nojan1/project-wrass/eda/audio-card/audio-card.kicad_pcb

## KiCad design eda/audio-card/audio-card.kicad_pcb (2023-07-22)

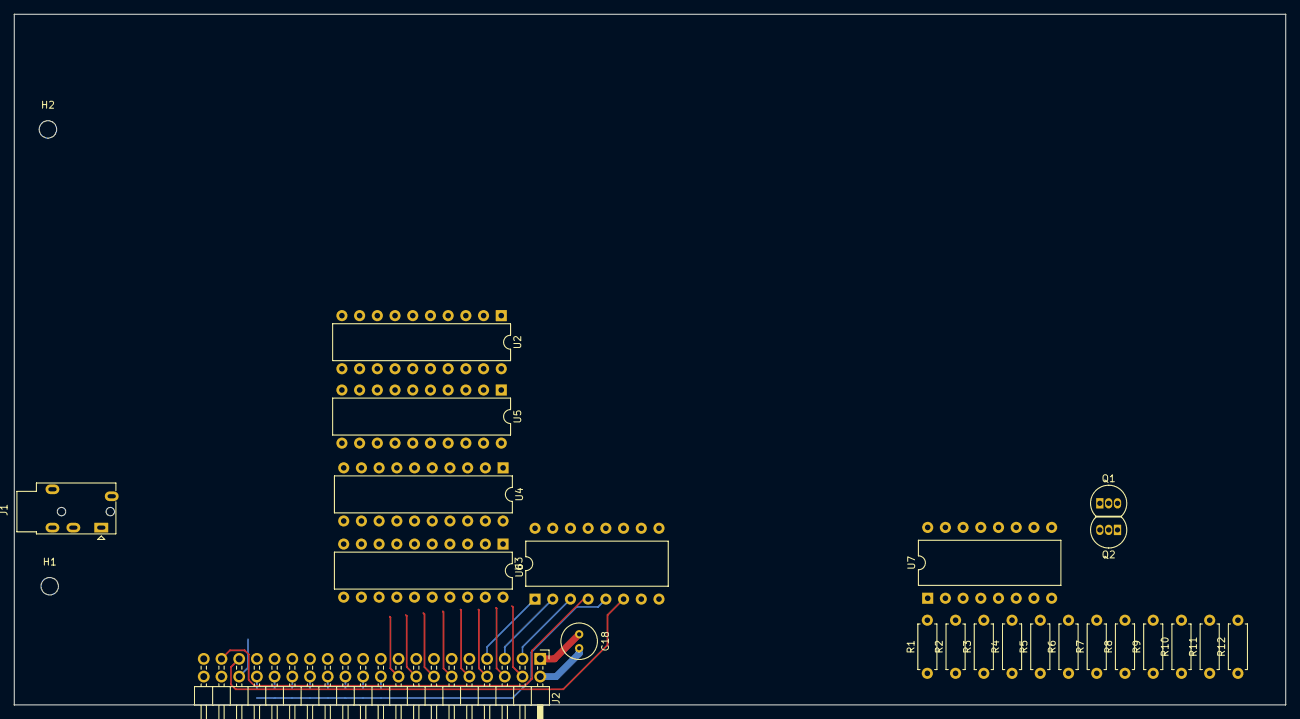
[picture p53: board audio-card.kicad_pcb from above]

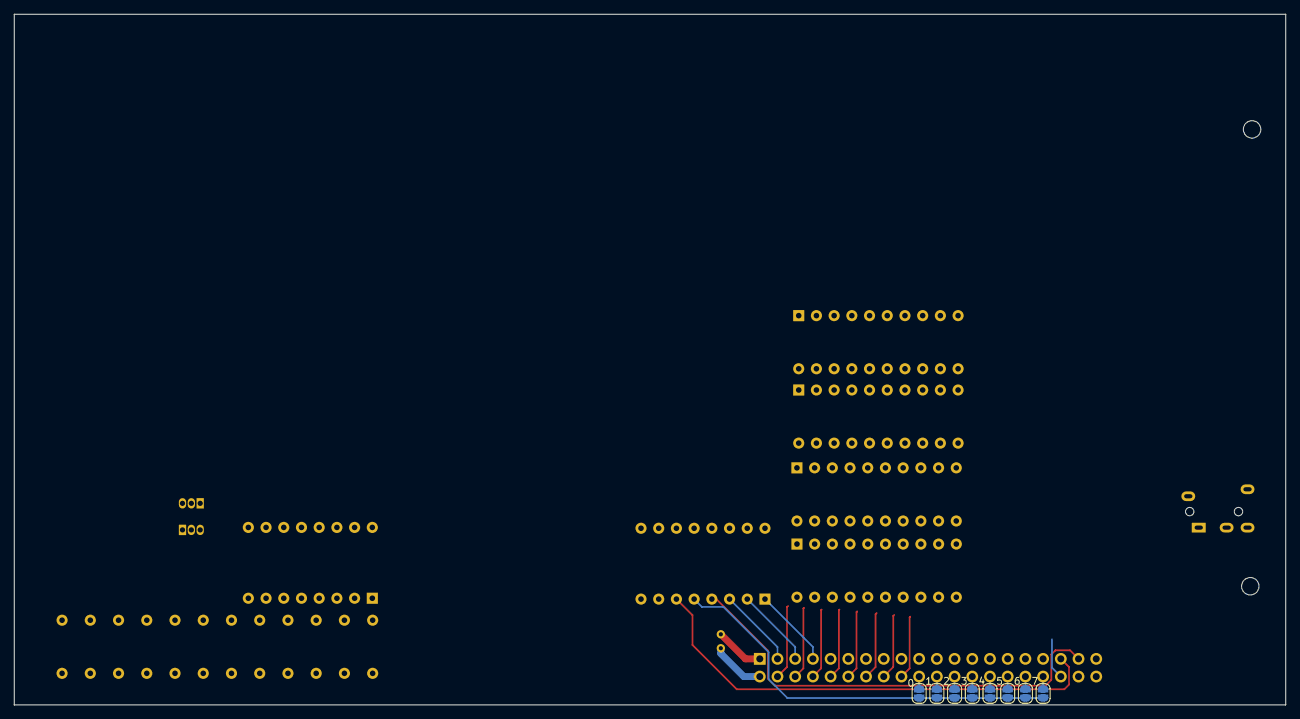
[picture p54: board audio-card.kicad_pcb from below]

Board: 2 copper layers, 182.4 x 99.1 mm, 33 parts (8 on the bottom side), 39 nets.

Parts:
C18: 100nf; C_Radial_D5.0mm_H7.0mm_P2.00mm
H1, H2: Bracket mounting; MountingHole_2.5mm
J1: AudioJack2_SwitchT; Jack_3.5mm_PJ320E_Horizontal
J2: Bus expansion; PinHeader_2x20_P2.54mm_Horizontal
JP1, JP2, JP3, JP4, JP5, JP6, JP7, JP8: SolderJumper_2_Open; SolderJumper-2_P1.3mm_Open_RoundedPad1.0x1.5mm
Q1, Q2: BC558; TO-92_Inline
R1, R2, R3: 100k; R_Axial_DIN0207_L6.3mm_D2.5mm_P7.62mm_Horizontal
R4: 100R; R_Axial_DIN0207_L6.3mm_D2.5mm_P7.62mm_Horizontal
R5: 200k; R_Axial_DIN0207_L6.3mm_D2.5mm_P7.62mm_Horizontal
R6: 33k; R_Axial_DIN0207_L6.3mm_D2.5mm_P7.62mm_Horizontal
R7, R8, R9: 10k; R_Axial_DIN0207_L6.3mm_D2.5mm_P7.62mm_Horizontal
R10, R11: 470k; R_Axial_DIN0207_L6.3mm_D2.5mm_P7.62mm_Horizontal
R12: 1k; R_Axial_DIN0207_L6.3mm_D2.5mm_P7.62mm_Horizontal
U2, U4, U5, U6: 74HCT574; DIP-20_W7.62mm
U3: 74HCT138; DIP-16_W10.16mm
U7: TL074; DIP-16_W10.16mm

Connections:
+12V: R1.1, R2.1
/Channel/D0: J2.4, U2.2 (D0), U4.2 (D0), U5.2 (D0), U6.2 (D0)
/Channel/D1: J2.6, U2.3 (D1), U4.3 (D1), U5.3 (D1), U6.3 (D1)
/Channel/D2: J2.8, U2.4 (D2), U4.4 (D2), U5.4 (D2), U6.4 (D2)
/Channel/D3: J2.10, U2.5 (D3), U4.5 (D3), U5.5 (D3), U6.5 (D3)
/Channel/D4: J2.12, U2.6 (D4), U4.6 (D4), U5.6 (D4), U6.6 (D4)
/Channel/D5: J2.14, U2.7 (D5), U4.7 (D5), U5.7 (D5), U6.7 (D5)
/Channel/D6: J2.16, U2.8 (D6), U4.8 (D6), U5.8 (D6), U6.8 (D6)
/Channel/D7: J2.18, U2.9 (D7), U4.9 (D7), U5.9 (D7), U6.9 (D7)
/Channel/~NoteLatch: U2.11 (Cp), U3.14 (O1)
/Channel/~OctaveLatch: U3.15 (O0), U6.11 (Cp)
/Channel/~VolumeLatch: U3.13 (O2), U4.11 (Cp)
/Expansion/A0: J2.3, U3.3 (A2)
/Expansion/A1: J2.5, U3.2 (A1)
/Expansion/A2: J2.7, U3.1 (A0)
/Expansion/Clock: J2.35, U3.6 (E3)
/Expansion/GND: C18.2, J2.2
/Expansion/R~W: J2.37, U3.4 (E1)
/Expansion/VCC: C18.1, J2.1
/Expansion/~CS: JP1.2 (B), JP2.2 (B), JP3.2 (B), JP4.2 (B), JP5.2 (B), JP6.2 (B), JP7.2 (B), JP8.2 (B), U3.5 (E2)
GND: Q2.2 (B), R4.2, R10.2, U2.1 (OE), U2.10 (GND), U4.1 (OE), U4.10 (GND), U5.1 (OE), U5.10 (GND), U6.1 (OE), U6.10 (GND), U7.3 (+)
unnamed: J2.20, JP1.1 (A)
unnamed: J2.22, JP2.1 (A)
unnamed: J2.24, JP3.1 (A)
unnamed: J2.26, JP4.1 (A)
unnamed: J2.28, JP5.1 (A)
unnamed: J2.30, JP6.1 (A)
unnamed: J2.32, JP7.1 (A)
unnamed: J2.34, JP8.1 (A)
unnamed: Q1.2 (B), R3.2, R4.1
unnamed: Q1.1 (C), R1.2, R7.1
unnamed: Q1.3 (E), Q2.3 (E), R9.1
unnamed: Q2.1 (C), R2.2, R8.1
unnamed: R6.2, R9.2, U7.1
unnamed: R11.2, R12.1, U7.7
unnamed: R5.1, R6.1, U7.2 (-)
unnamed: R8.2, R10.1, U7.5 (+)
unnamed: R7.2, R11.1, U7.6 (-)
VCC: U2.20 (VCC), U4.20 (VCC), U5.20 (VCC), U6.20 (VCC)
