nojan1/project-wrass/eda/expansion-backplane/expansion-backplane.kicad_pcb

## KiCad design eda/expansion-backplane/expansion-backplane.kicad_pcb (2023-07-08)

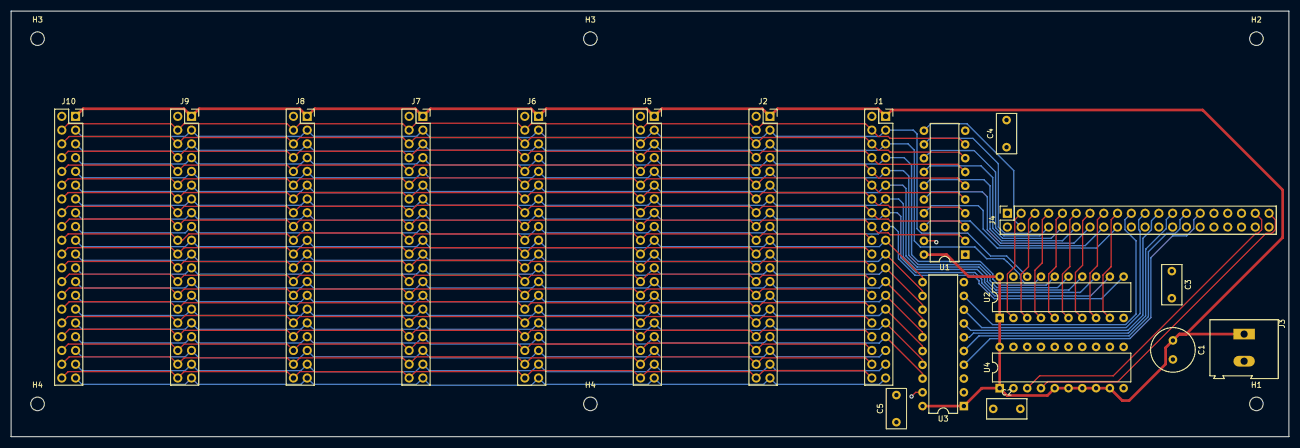
[picture p55: board expansion-backplane.kicad_pcb from above]

Board: 2 copper layers, 235.7 x 78.5 mm, 25 parts (0 on the bottom side), 67 nets.

Parts:
C1: 1u; C_Radial_D8.0mm_H7.0mm_P3.50mm
C2, C3, C4, C5: 100nf; C_Rect_L7.2mm_W3.5mm_P5.00mm_FKS2_FKP2_MKS2_MKP2
H1, H2, H3, H3#2, H4, H4#2: MountingHole; MountingHole_2.5mm
J1: OUT1; PinSocket_2x20_P2.54mm_Vertical
J2: OUT5; PinSocket_2x20_P2.54mm_Vertical
J3: PWR; TerminalBlock_Altech_AK300-2_P5.00mm
J4: IN; PinSocket_2x20_P2.54mm_Vertical
J5: OUT2; PinSocket_2x20_P2.54mm_Vertical
J6: OUT6; PinSocket_2x20_P2.54mm_Vertical
J7: OUT3; PinSocket_2x20_P2.54mm_Vertical
J8: OUT7; PinSocket_2x20_P2.54mm_Vertical
J9: OUT4; PinSocket_2x20_P2.54mm_Vertical
J10: OUT8; PinSocket_2x20_P2.54mm_Vertical
U1, U2, U3, U4: 74HCT245; DIP-20_W7.62mm

Connections:
/IA0: J4.3, U2.2 (A0)
/IA1: J4.5, U2.3 (A1)
/IA2: J4.7, U2.4 (A2)
/IA3: J4.9, U2.5 (A3)
/IA4: J4.11, U2.6 (A4)
/IA5: J4.13, U2.7 (A5)
/IA6: J4.15, U2.8 (A6)
/IA7: J4.17, U2.9 (A7)
/IA8: J4.19, U3.9 (A7)
/IA9: J4.21, U3.8 (A6)
/IA10: J4.23, U3.7 (A5)
/IA11: J4.25, U3.6 (A4)
/IA12: J4.27, U3.5 (A3)
/IA13: J4.29, U3.4 (A2)
/IA14: J4.31, U3.3 (A1)
/IA15: J4.33, U3.2 (A0)
/IClock: J4.35, U4.2 (A0)
/ID0: J4.4, U1.11 (B7)
/ID1: J4.6, U1.12 (B6)
/ID2: J4.8, U1.13 (B5)
/ID3: J4.10, U1.14 (B4)
/ID4: J4.12, U1.15 (B3)
/ID5: J4.14, U1.16 (B2)
/ID6: J4.16, U1.17 (B1)
/ID7: J4.18, U1.18 (B0)
/IR~W: J4.37, U1.1 (A->B), U4.3 (A1)
/I~DMA: J4.39, U4.4 (A2)
A0: J1.3, J2.3, J5.3, J6.3, J7.3, J8.3, J9.3, J10.3, U2.18 (B0)
A1: J1.5, J2.5, J5.5, J6.5, J7.5, J8.5, J9.5, J10.5, U2.17 (B1)
A2: J1.7, J2.7, J5.7, J6.7, J7.7, J8.7, J9.7, J10.7, U2.16 (B2)
A3: J1.9, J2.9, J5.9, J6.9, J7.9, J8.9, J9.9, J10.9, U2.15 (B3)
A4: J1.11, J2.11, J5.11, J6.11, J7.11, J8.11, J9.11, J10.11, U2.14 (B4)
A5: J1.13, J2.13, J5.13, J6.13, J7.13, J8.13, J9.13, J10.13, U2.13 (B5)
A6: J1.15, J2.15, J5.15, J6.15, J7.15, J8.15, J9.15, J10.15, U2.12 (B6)
A7: J1.17, J2.17, J5.17, J6.17, J7.17, J8.17, J9.17, J10.17, U2.11 (B7)
A8: J1.19, J2.19, J5.19, J6.19, J7.19, J8.19, J9.19, J10.19, U3.11 (B7)
A9: J1.21, J2.21, J5.21, J6.21, J7.21, J8.21, J9.21, J10.21, U3.12 (B6)
A10: J1.23, J2.23, J5.23, J6.23, J7.23, J8.23, J9.23, J10.23, U3.13 (B5)
A11: J1.25, J2.25, J5.25, J6.25, J7.25, J8.25, J9.25, J10.25, U3.14 (B4)
A12: J1.27, J2.27, J5.27, J6.27, J7.27, J8.27, J9.27, J10.27, U3.15 (B3)
A13: J1.29, J2.29, J5.29, J6.29, J7.29, J8.29, J9.29, J10.29, U3.16 (B2)
A14: J1.31, J2.31, J5.31, J6.31, J7.31, J8.31, J9.31, J10.31, U3.17 (B1)
A15: J1.33, J2.33, J5.33, J6.33, J7.33, J8.33, J9.33, J10.33, U3.18 (B0)
Clock: J1.35, J2.35, J5.35, J6.35, J7.35, J8.35, J9.35, J10.35, U4.18 (B0)
D0: J1.4, J2.4, J5.4, J6.4, J7.4, J8.4, J9.4, J10.4, U1.9 (A7)
D1: J1.6, J2.6, J5.6, J6.6, J7.6, J8.6, J9.6, J10.6, U1.8 (A6)
D2: J1.8, J2.8, J5.8, J6.8, J7.8, J8.8, J9.8, J10.8, U1.7 (A5)
D3: J1.10, J2.10, J5.10, J6.10, J7.10, J8.10, J9.10, J10.10, U1.6 (A4)
D4: J1.12, J2.12, J5.12, J6.12, J7.12, J8.12, J9.12, J10.12, U1.5 (A3)
D5: J1.14, J2.14, J5.14, J6.14, J7.14, J8.14, J9.14, J10.14, U1.4 (A2)
D6: J1.16, J2.16, J5.16, J6.16, J7.16, J8.16, J9.16, J10.16, U1.3 (A1)
D7: J1.18, J2.18, J5.18, J6.18, J7.18, J8.18, J9.18, J10.18, U1.2 (A0)
GND: C1.2, C2.2, C3.2, C4.2, C5.2, J1.2, J2.2, J3.2, J4.2, J5.2, J6.2, J7.2, J8.2, J9.2, J10.2, U1.10 (GND), U1.19 (CE), U2.10 (GND), U2.19 (CE), U3.10 (GND), U3.19 (CE), U4.10 (GND), U4.19 (CE)
IO0: J1.20, J2.20, J4.20, J5.20, J6.20, J7.20, J8.20, J9.20, J10.20
IO1: J1.22, J2.22, J4.22, J5.22, J6.22, J7.22, J8.22, J9.22, J10.22
IO2: J1.24, J2.24, J4.24, J5.24, J6.24, J7.24, J8.24, J9.24, J10.24
IO3: J1.26, J2.26, J4.26, J5.26, J6.26, J7.26, J8.26, J9.26, J10.26
IO4: J1.28, J2.28, J4.28, J5.28, J6.28, J7.28, J8.28, J9.28, J10.28
IO5: J1.30, J2.30, J4.30, J5.30, J6.30, J7.30, J8.30, J9.30, J10.30
IO6: J1.32, J2.32, J4.32, J5.32, J6.32, J7.32, J8.32, J9.32, J10.32
IO7: J1.34, J2.34, J4.34, J5.34, J6.34, J7.34, J8.34, J9.34, J10.34
R~W: J1.37, J2.37, J5.37, J6.37, J7.37, J8.37, J9.37, J10.37, U4.17 (B1)
VCC: C1.1, C2.1, C3.1, C4.1, C5.1, J1.1, J2.1, J3.1, J5.1, J6.1, J7.1, J8.1, J9.1, J10.1, U1.20 (VCC), U2.1 (A->B), U2.20 (VCC), U3.1 (A->B), U3.20 (VCC), U4.1 (A->B), U4.5 (A3), U4.6 (A4), U4.7 (A5), U4.8 (A6), U4.9 (A7), U4.20 (VCC)
~DMA: J1.39, J2.39, J5.39, J6.39, J7.39, J8.39, J9.39, J10.39, U4.16 (B2)
~IRQ: J1.40, J2.40, J4.40, J5.40, J6.40, J7.40, J8.40, J9.40, J10.40
~NMI: J1.38, J2.38, J4.38, J5.38, J6.38, J7.38, J8.38, J9.38, J10.38
~RST: J1.36, J2.36, J4.36, J5.36, J6.36, J7.36, J8.36, J9.36, J10.36
