nojan1/project-wrass/eda/expansion-breakout/expansion-breakout.kicad_pcb

## KiCad design eda/expansion-breakout/expansion-breakout.kicad_pcb (2023-05-07)

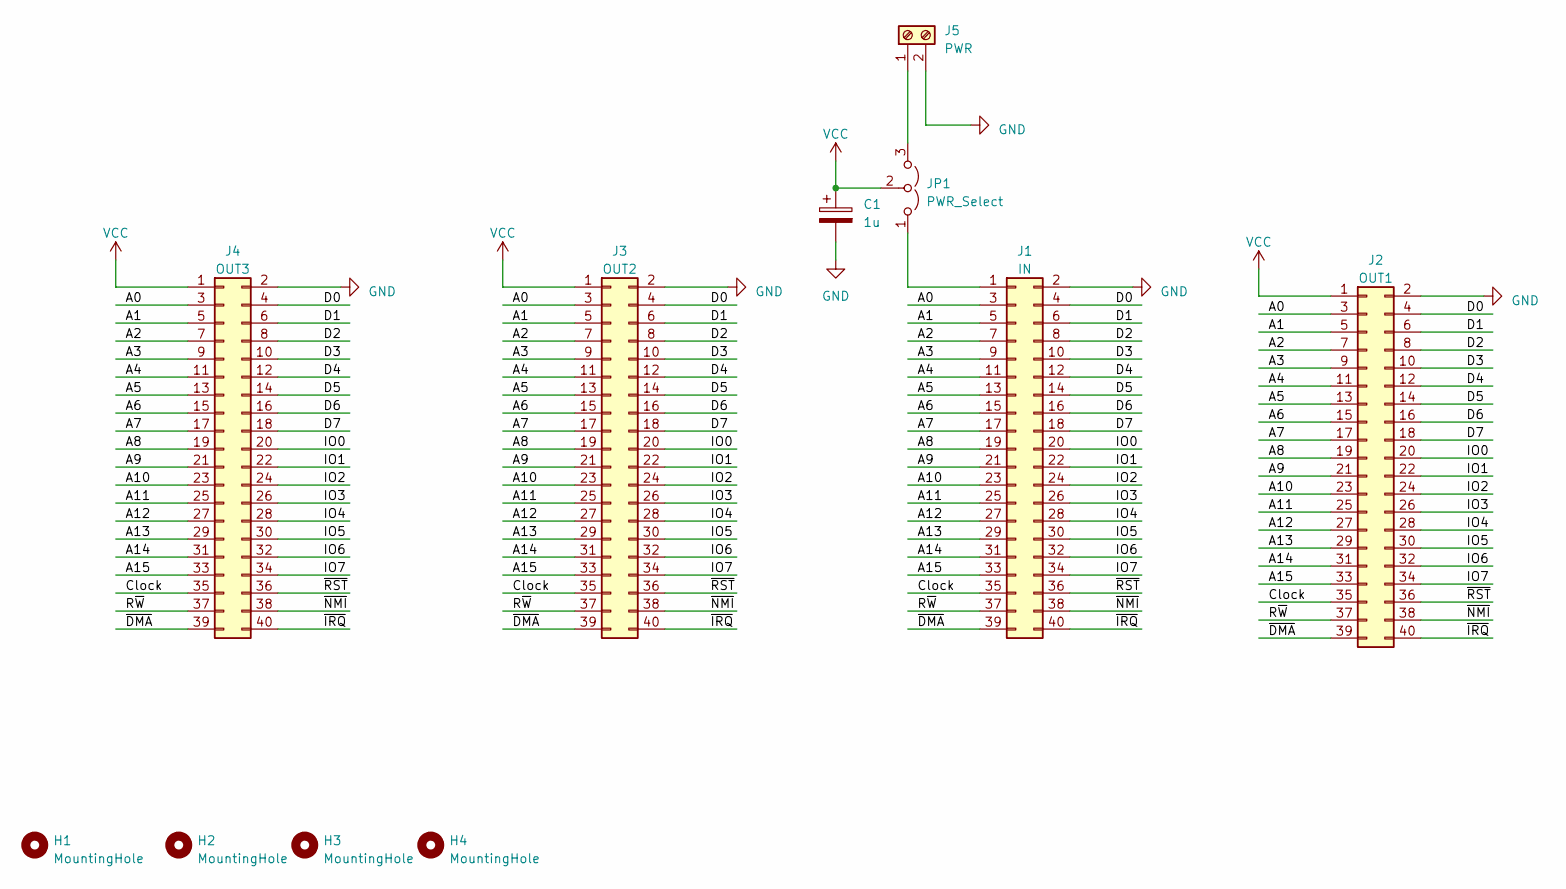
[picture p56: schematic expansion-breakout.kicad_sch]

Parts:
C1: 1u; C_Radial_D8.0mm_H7.0mm_P3.50mm
H1, H2, H3, H4: MountingHole; MountingHole_2.5mm
J1: IN; PinHeader_2x20_P2.54mm_Vertical
J2: OUT1; PinHeader_2x20_P2.54mm_Vertical
J3: OUT2; PinSocket_2x20_P2.54mm_Vertical
J4: OUT3; PinSocket_2x20_P2.54mm_Vertical
J5: PWR; TerminalBlock_Altech_AK300-2_P5.00mm
JP1: PWR_Select; PinHeader_1x03_P2.54mm_Vertical

Connections:
/A0: J1.3, J2.3, J3.3, J4.3
/A1: J1.5, J2.5, J3.5, J4.5
/A2: J1.7, J2.7, J3.7, J4.7
/A3: J1.9, J2.9, J3.9, J4.9
/A4: J1.11, J2.11, J3.11, J4.11
/A5: J1.13, J2.13, J3.13, J4.13
/A6: J1.15, J2.15, J3.15, J4.15
/A7: J1.17, J2.17, J3.17, J4.17
/A8: J1.19, J2.19, J3.19, J4.19
/A9: J1.21, J2.21, J3.21, J4.21
/A10: J1.23, J2.23, J3.23, J4.23
/A11: J1.25, J2.25, J3.25, J4.25
/A12: J1.27, J2.27, J3.27, J4.27
/A13: J1.29, J2.29, J3.29, J4.29
/A14: J1.31, J2.31, J3.31, J4.31
/A15: J1.33, J2.33, J3.33, J4.33
/Clock: J1.35, J2.35, J3.35, J4.35
/D0: J1.4, J2.4, J3.4, J4.4
/D1: J1.6, J2.6, J3.6, J4.6
/D2: J1.8, J2.8, J3.8, J4.8
/D3: J1.10, J2.10, J3.10, J4.10
/D4: J1.12, J2.12, J3.12, J4.12
/D5: J1.14, J2.14, J3.14, J4.14
/D6: J1.16, J2.16, J3.16, J4.16
/D7: J1.18, J2.18, J3.18, J4.18
/IO0: J1.20, J2.20, J3.20, J4.20
/IO1: J1.22, J2.22, J3.22, J4.22
/IO2: J1.24, J2.24, J3.24, J4.24
/IO3: J1.26, J2.26, J3.26, J4.26
/IO4: J1.28, J2.28, J3.28, J4.28
/IO5: J1.30, J2.30, J3.30, J4.30
/IO6: J1.32, J2.32, J3.32, J4.32
/IO7: J1.34, J2.34, J3.34, J4.34
/R~W: J1.37, J2.37, J3.37, J4.37
/~DMA: J1.39, J2.39, J3.39, J4.39
/~IRQ: J1.40, J2.40, J3.40, J4.40
/~NMI: J1.38, J2.38, J3.38, J4.38
/~RST: J1.36, J2.36, J3.36, J4.36
GND: C1.2, J1.2, J2.2, J3.2, J4.2, J5.2
unnamed: J1.1, JP1.1 (A)
unnamed: J5.1, JP1.3 (B)
VCC: C1.1, J2.1, J3.1, J4.1, JP1.2 (C)

Board: 2 copper layers, 11 parts (2 on the bottom side), 42 nets, no tracks yet.
