nojan1/project-wrass/eda/keyboard/keyboard.kicad_pcb

## KiCad design eda/keyboard/keyboard.kicad_pcb (2023-05-06)

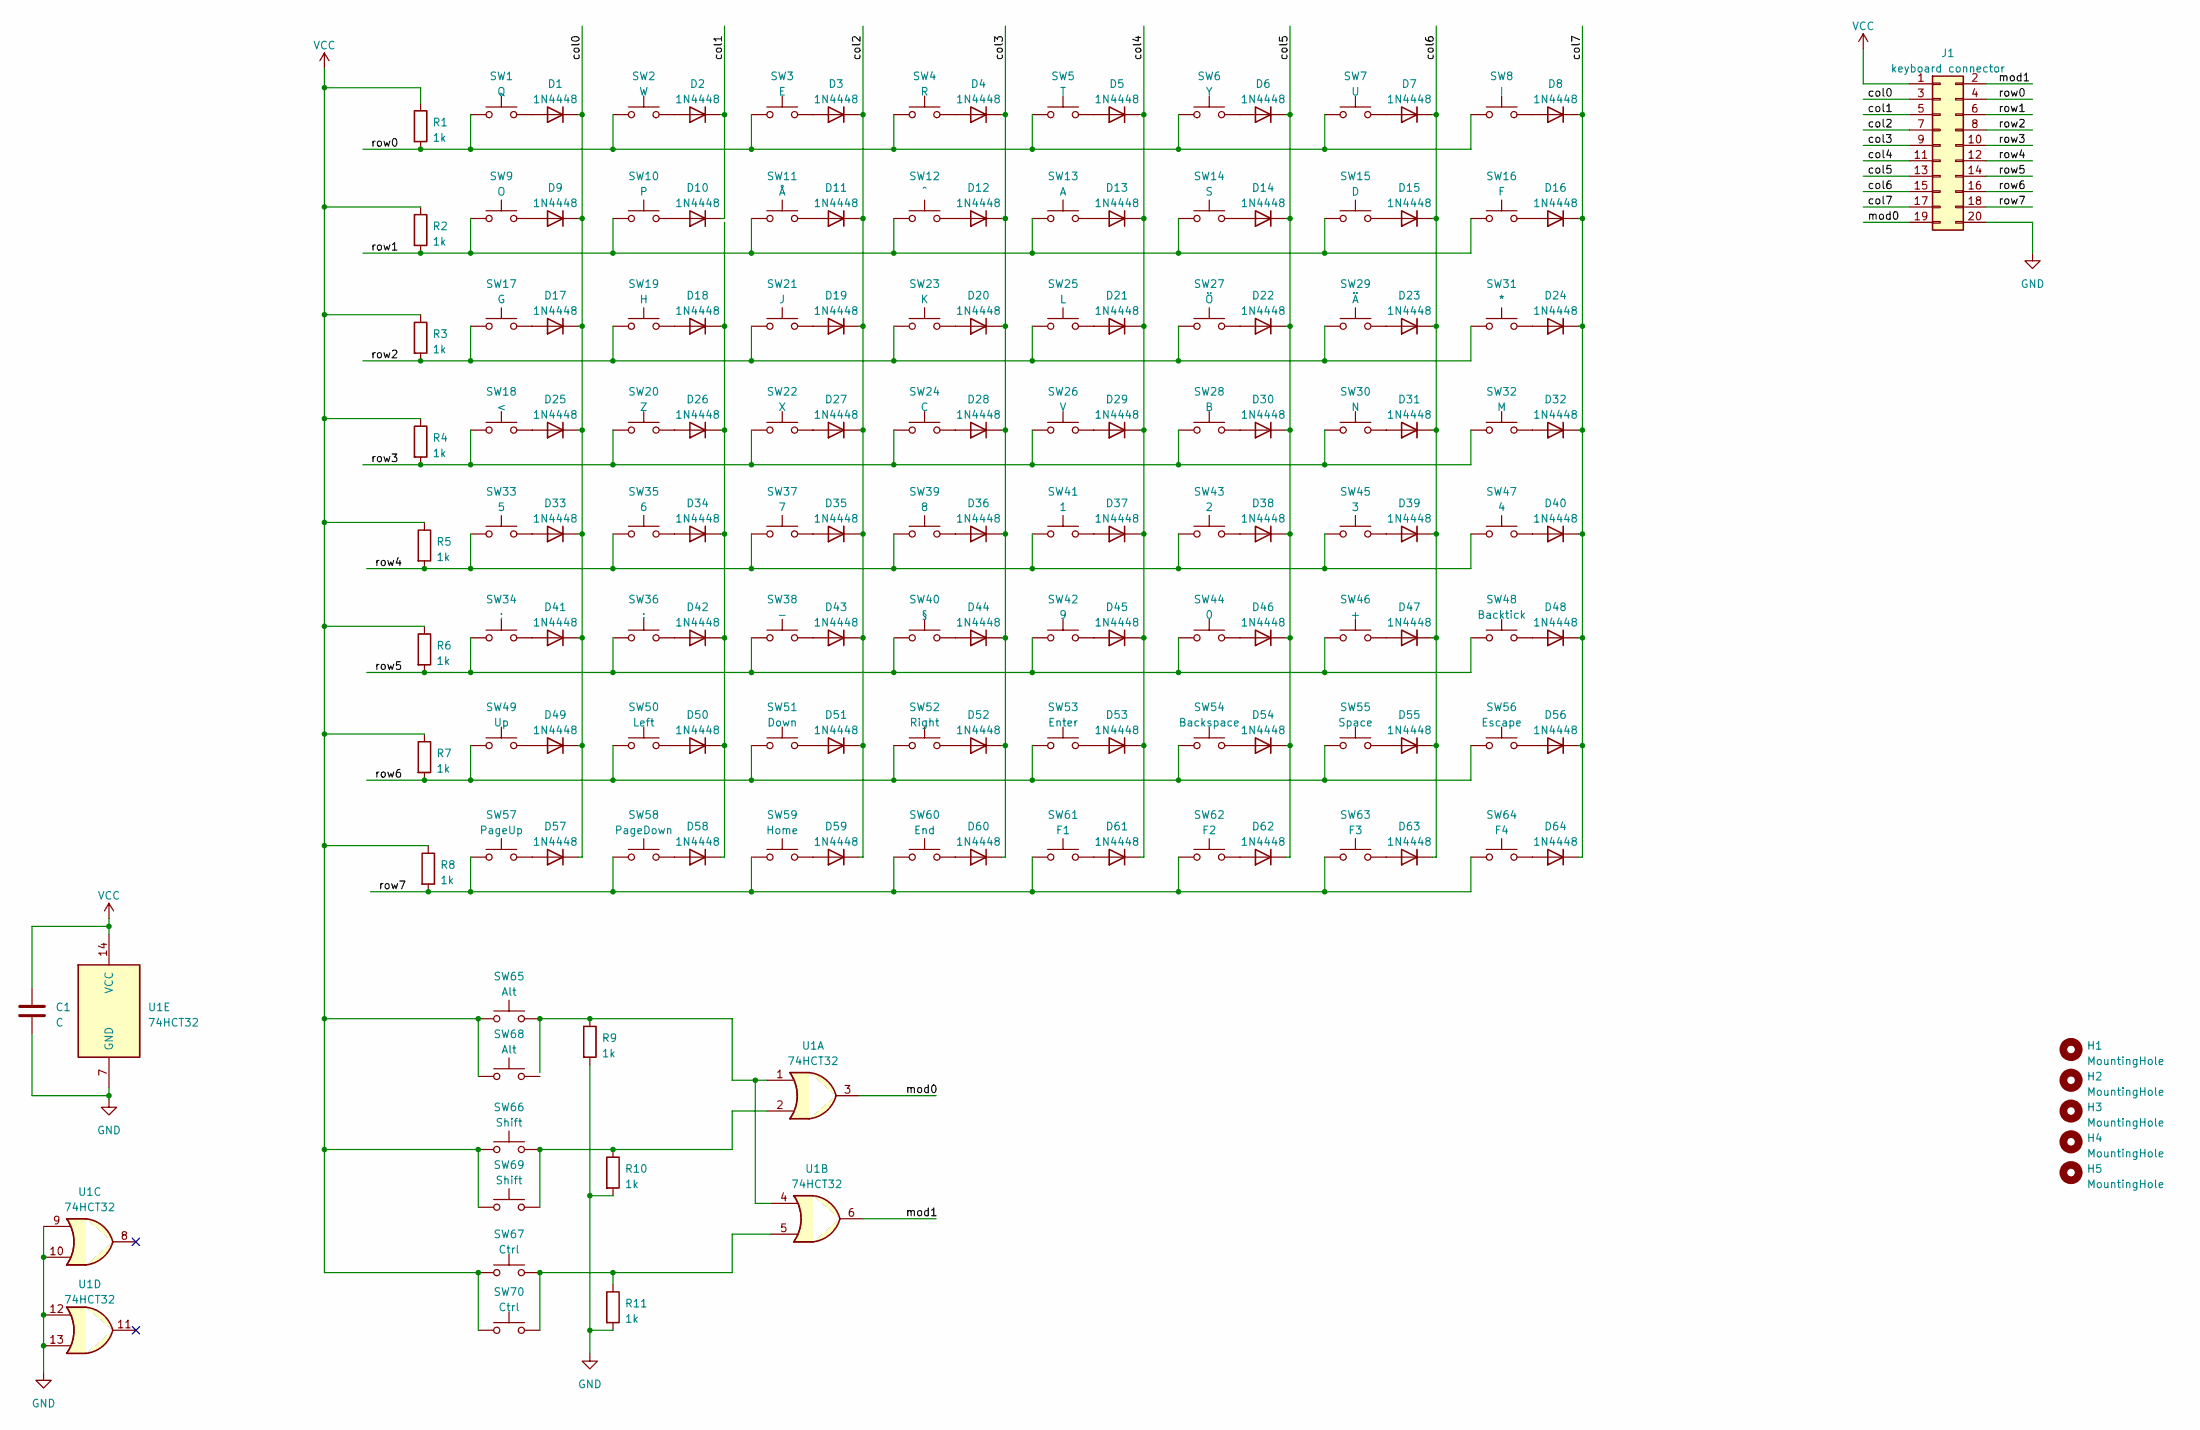
[picture p57: schematic keyboard.kicad_sch]

Parts:
C1: C
D1, D2, D3, D4, D5, D6, D7, D8, D9, D10, D11, D12, D13, D14, D15, D16, D17, D18, D19, D20, D21, D22, D23, D24, D25, D26, D27, D28, D29, D30, D31, D32, D33, D34, D35, D36, D37, D38, D39, D40, D41, D42, D43, D44, D45, D46, D47, D48, D49, D50, D51, D52, D53, D54, D55, D56, D57, D58, D59, D60, D61, D62, D63, D64: 1N4448; D_DO-35_SOD27_P7.62mm_Horizontal
H1, H2, H3, H4, H5: MountingHole; MountingHole_2.5mm
J1: keyboard connector; PinSocket_2x10_P2.54mm_Horizontal
R1, R2, R3, R4, R5, R6, R7, R8, R9, R10, R11: 1k
SW1: Q; SW_Cherry_MX_PCB_1.00u
SW2: W; SW_Cherry_MX_PCB_1.00u
SW3: E; SW_Cherry_MX_PCB_1.00u
SW4: R; SW_Cherry_MX_PCB_1.00u
SW5: T; SW_Cherry_MX_PCB_1.00u
SW6: Y; SW_Cherry_MX_PCB_1.00u
SW7: U; SW_Cherry_MX_PCB_1.00u
SW8: I; SW_Cherry_MX_PCB_1.00u
SW9: O; SW_Cherry_MX_PCB_1.00u
SW10: P; SW_Cherry_MX_PCB_1.00u
SW11: Å; SW_Cherry_MX_PCB_1.00u
SW12: ^; SW_Cherry_MX_PCB_1.00u
SW13: A; SW_Cherry_MX_PCB_1.00u
SW14: S; SW_Cherry_MX_PCB_1.00u
SW15: D; SW_Cherry_MX_PCB_1.00u
SW16: F; SW_Cherry_MX_PCB_1.00u
SW17: G; SW_Cherry_MX_PCB_1.00u
SW18: <; SW_Cherry_MX_PCB_1.00u
SW19: H; SW_Cherry_MX_PCB_1.00u
SW20: Z; SW_Cherry_MX_PCB_1.00u
SW21: J; SW_Cherry_MX_PCB_1.00u
SW22: X; SW_Cherry_MX_PCB_1.00u
SW23: K; SW_Cherry_MX_PCB_1.00u
SW24: C; SW_Cherry_MX_PCB_1.00u
SW25: L; SW_Cherry_MX_PCB_1.00u
SW26: V; SW_Cherry_MX_PCB_1.00u
SW27: Ö; SW_Cherry_MX_PCB_1.00u
SW28: B; SW_Cherry_MX_PCB_1.00u
SW29: Ä; SW_Cherry_MX_PCB_1.00u
SW30: N; SW_Cherry_MX_PCB_1.00u
SW31: *; SW_Cherry_MX_PCB_1.00u
SW32: M; SW_Cherry_MX_PCB_1.00u
SW33: 5; SW_Cherry_MX_PCB_1.00u
SW34: ;; SW_Cherry_MX_PCB_1.00u
SW35: 6; SW_Cherry_MX_PCB_1.00u
SW36: :; SW_Cherry_MX_PCB_1.00u
SW37: 7; SW_Cherry_MX_PCB_1.00u
SW38: -; SW_Cherry_MX_PCB_1.00u
SW39: 8; SW_Cherry_MX_PCB_1.00u
SW40: §; SW_Cherry_MX_PCB_1.00u
SW41: 1; SW_Cherry_MX_PCB_1.00u
SW42: 9; SW_Cherry_MX_PCB_1.00u
SW43: 2; SW_Cherry_MX_PCB_1.00u
SW44: 0; SW_Cherry_MX_PCB_1.00u
SW45: 3; SW_Cherry_MX_PCB_1.00u
SW46: +; SW_Cherry_MX_PCB_1.00u
SW47: 4; SW_Cherry_MX_PCB_1.00u
SW48: Backtick; SW_Cherry_MX_PCB_1.00u
SW49: Up; SW_Cherry_MX_PCB_1.00u
SW50: Left; SW_Cherry_MX_PCB_1.00u
SW51: Down; SW_Cherry_MX_PCB_1.00u
SW52: Right; SW_Cherry_MX_PCB_1.00u
SW53: Enter; SW_Cherry_MX_PCB_ISOEnter
SW54: Backspace; SW_Cherry_MX_PCB_2.00u
SW55: Space; SW_Cherry_MX_PCB_1.00u
SW56: Escape; SW_Cherry_MX_PCB_1.00u
SW57: PageUp; SW_Cherry_MX_PCB_1.00u
SW58: PageDown; SW_Cherry_MX_PCB_1.00u
SW59: Home; SW_Cherry_MX_PCB_1.00u
SW60: End; SW_Cherry_MX_PCB_1.00u
SW61: F1; SW_Cherry_MX_PCB_1.00u
SW62: F2; SW_Cherry_MX_PCB_1.00u
SW63: F3; SW_Cherry_MX_PCB_1.00u
SW64: F4; SW_Cherry_MX_PCB_1.00u
SW65, SW68: Alt; SW_Cherry_MX_PCB_1.25u
SW66: Shift; SW_Cherry_MX_PCB_1.25u
SW67, SW70: Ctrl; SW_Cherry_MX_PCB_1.25u
SW69: Shift; SW_Cherry_MX_PCB_2.75u
U1: 74HCT32; DIP-14_W10.16mm

Connections:
/col0: D1.1 (K), D9.1 (K), D17.1 (K), D25.1 (K), D33.1 (K), D41.1 (K), D49.1 (K), D57.1 (K), J1.3
/col1: D2.1 (K), D10.1 (K), J1.5
/col2: D3.1 (K), D11.1 (K), D19.1 (K), D27.1 (K), D35.1 (K), D43.1 (K), D51.1 (K), D59.1 (K), J1.7
/col3: D4.1 (K), D12.1 (K), D20.1 (K), D28.1 (K), D36.1 (K), D44.1 (K), D52.1 (K), D60.1 (K), J1.9
/col4: D5.1 (K), D13.1 (K), D21.1 (K), D29.1 (K), D37.1 (K), D45.1 (K), D53.1 (K), D61.1 (K), J1.11
/col5: D6.1 (K), D14.1 (K), D22.1 (K), D30.1 (K), D38.1 (K), D46.1 (K), D54.1 (K), D62.1 (K), J1.13
/col6: D7.1 (K), D15.1 (K), D23.1 (K), D31.1 (K), D39.1 (K), D47.1 (K), D55.1 (K), D63.1 (K), J1.15
/col7: D8.1 (K), D16.1 (K), D24.1 (K), D32.1 (K), D40.1 (K), D48.1 (K), D56.1 (K), D64.1 (K), J1.17
/mod0: J1.19, U1.3
/mod1: J1.2, U1.6
/row0: J1.4, R1.2, SW1.1, SW2.1, SW3.1, SW4.1, SW5.1, SW6.1, SW7.1, SW8.1
/row1: J1.6, R2.2, SW9.1, SW10.1, SW11.1, SW12.1, SW13.1, SW14.1, SW15.1, SW16.1
/row2: J1.8, R3.2, SW17.1, SW19.1, SW21.1, SW23.1, SW25.1, SW27.1, SW29.1, SW31.1
/row3: J1.10, R4.2, SW18.1, SW20.1, SW22.1, SW24.1, SW26.1, SW28.1, SW30.1, SW32.1
/row4: J1.12, R5.2, SW33.1, SW35.1, SW37.1, SW39.1, SW41.1, SW43.1, SW45.1, SW47.1
/row5: J1.14, R6.2, SW34.1, SW36.1, SW38.1, SW40.1, SW42.1, SW44.1, SW46.1, SW48.1
/row6: J1.16, R7.2, SW49.1, SW50.1, SW51.1, SW52.1, SW53.1, SW54.1, SW55.1, SW56.1
/row7: J1.18, R8.2, SW57.1, SW58.1, SW59.1, SW60.1, SW61.1, SW62.1, SW63.1, SW64.1
GND: C1.2, J1.20, R9.2, R10.2, R11.2, U1.7 (GND), U1.9, U1.10, U1.12, U1.13
unnamed: D1.2 (A), SW1.2
unnamed: D2.2 (A), SW2.2
unnamed: D3.2 (A), SW3.2
unnamed: D4.2 (A), SW4.2
unnamed: D5.2 (A), SW5.2
unnamed: D6.2 (A), SW6.2
unnamed: D7.2 (A), SW7.2
unnamed: D8.2 (A), SW8.2
unnamed: D9.2 (A), SW9.2
unnamed: D10.2 (A), SW10.2
unnamed: D11.2 (A), SW11.2
unnamed: D12.2 (A), SW12.2
unnamed: D13.2 (A), SW13.2
unnamed: D14.2 (A), SW14.2
unnamed: D15.2 (A), SW15.2
unnamed: D16.2 (A), SW16.2
unnamed: D17.2 (A), SW17.2
unnamed: D18.2 (A), SW19.2
unnamed: D18.1 (K), D26.1 (K), D34.1 (K), D42.1 (K), D50.1 (K), D58.1 (K)
unnamed: D19.2 (A), SW21.2
unnamed: D20.2 (A), SW23.2
unnamed: D21.2 (A), SW25.2
unnamed: D22.2 (A), SW27.2
unnamed: D23.2 (A), SW29.2
unnamed: D24.2 (A), SW31.2
unnamed: D25.2 (A), SW18.2
unnamed: D26.2 (A), SW20.2
unnamed: D27.2 (A), SW22.2
unnamed: D28.2 (A), SW24.2
unnamed: D29.2 (A), SW26.2
unnamed: D30.2 (A), SW28.2
unnamed: D31.2 (A), SW30.2
unnamed: D32.2 (A), SW32.2
unnamed: D33.2 (A), SW33.2
unnamed: D34.2 (A), SW35.2
unnamed: D35.2 (A), SW37.2
unnamed: D36.2 (A), SW39.2
unnamed: D37.2 (A), SW41.2
unnamed: D38.2 (A), SW43.2
unnamed: D39.2 (A), SW45.2
unnamed: D40.2 (A), SW47.2
unnamed: D41.2 (A), SW34.2
unnamed: D42.2 (A), SW36.2
unnamed: D43.2 (A), SW38.2
unnamed: D44.2 (A), SW40.2
unnamed: D45.2 (A), SW42.2
unnamed: D46.2 (A), SW44.2
unnamed: D47.2 (A), SW46.2
unnamed: D48.2 (A), SW48.2
unnamed: D49.2 (A), SW49.2
unnamed: D50.2 (A), SW50.2
unnamed: D51.2 (A), SW51.2
unnamed: D52.2 (A), SW52.2
unnamed: D53.2 (A), SW53.2
unnamed: D54.2 (A), SW54.2
unnamed: D55.2 (A), SW55.2
unnamed: D56.2 (A), SW56.2
unnamed: D57.2 (A), SW57.2
unnamed: D58.2 (A), SW58.2
unnamed: D59.2 (A), SW59.2
unnamed: D60.2 (A), SW60.2
unnamed: D61.2 (A), SW61.2
unnamed: D62.2 (A), SW62.2
unnamed: D63.2 (A), SW63.2
unnamed: D64.2 (A), SW64.2
unnamed: R9.1, SW65.2, U1.1, U1.4
unnamed: R10.1, SW66.2, SW69.2, U1.2
unnamed: R11.1, SW67.2, SW70.2, U1.5
VCC: C1.1, J1.1, R1.1, R2.1, R3.1, R4.1, R5.1, R6.1, R7.1, R8.1, SW65.1, SW66.1, SW67.1, SW68.1, SW69.1, SW70.1, U1.14 (VCC)

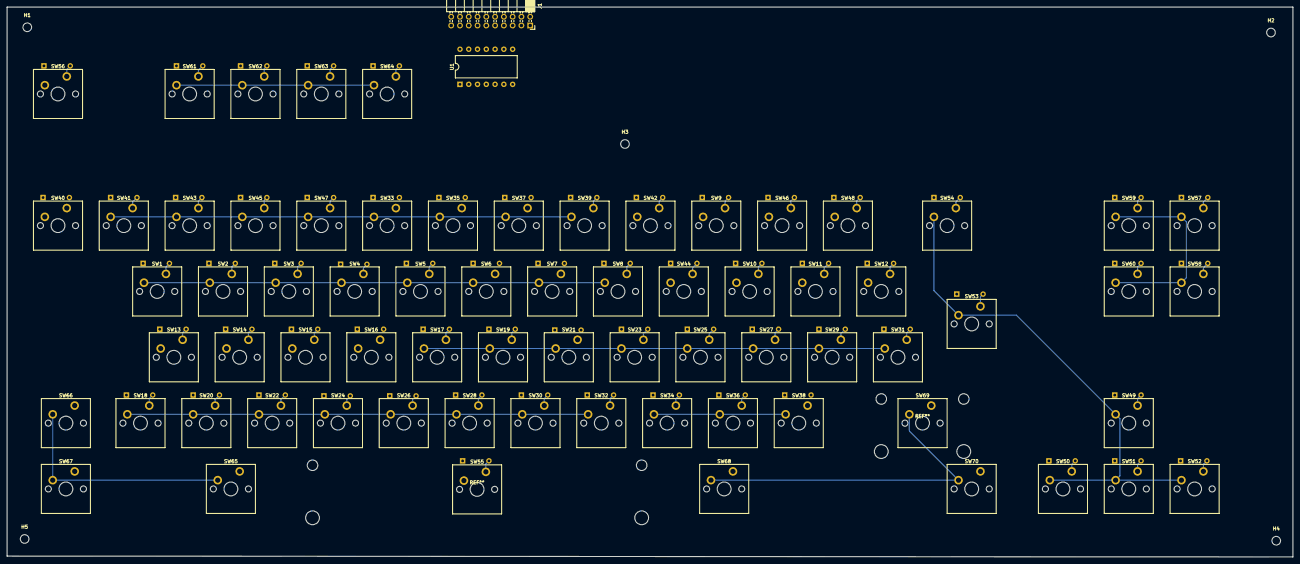
[picture p58: board keyboard.kicad_pcb from above]

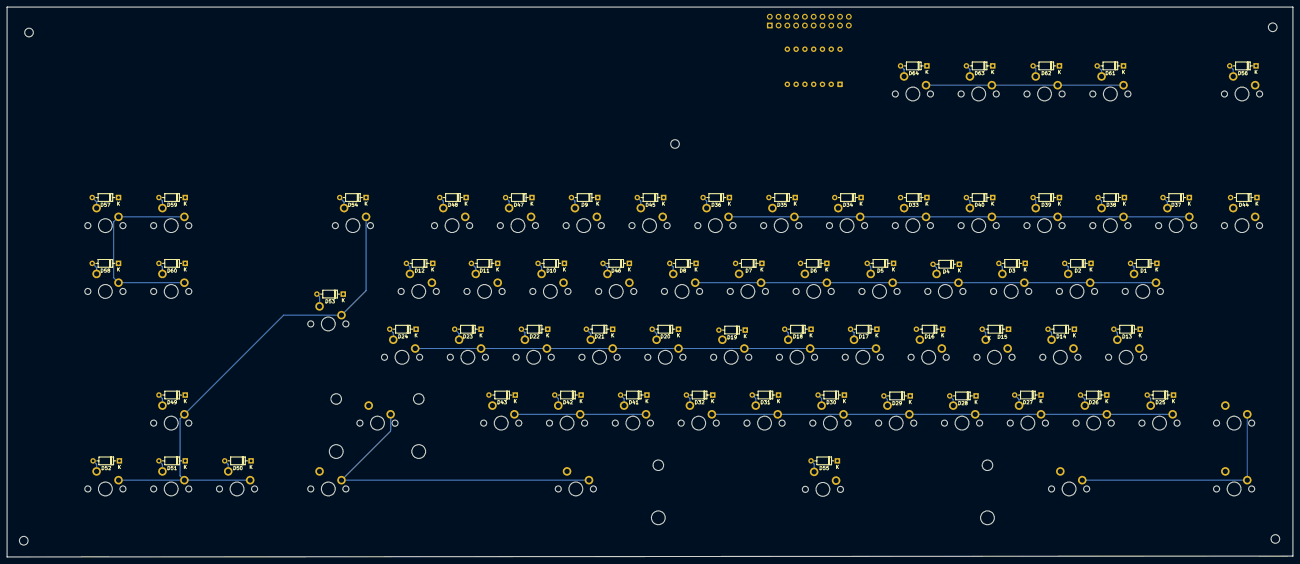
[picture p59: board keyboard.kicad_pcb from below]

Board: 2 copper layers, 372.1 x 159.1 mm, 141 parts (64 on the bottom side), 88 nets.
